Keriz/eeaic-2022-pll/pll.kicad_sch

## KiCad design pll.kicad_sch (2022-06-06)

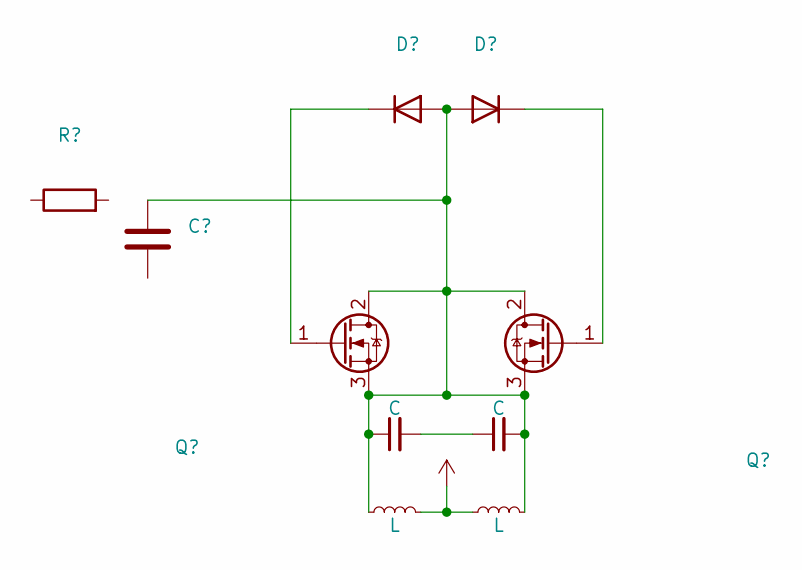
[picture p67: schematic pll.kicad_sch]

Parts:
C: (no value)
L: (no value)

Connections:
unnamed: C.1, C.2, L.1, L.2
unnamed: L.1, L.2
