Keriz/eeaic-2022-pll/PLL/PLL.kicad_sch

## KiCad design PLL/PLL.kicad_sch (2022-11-11, an earlier design)

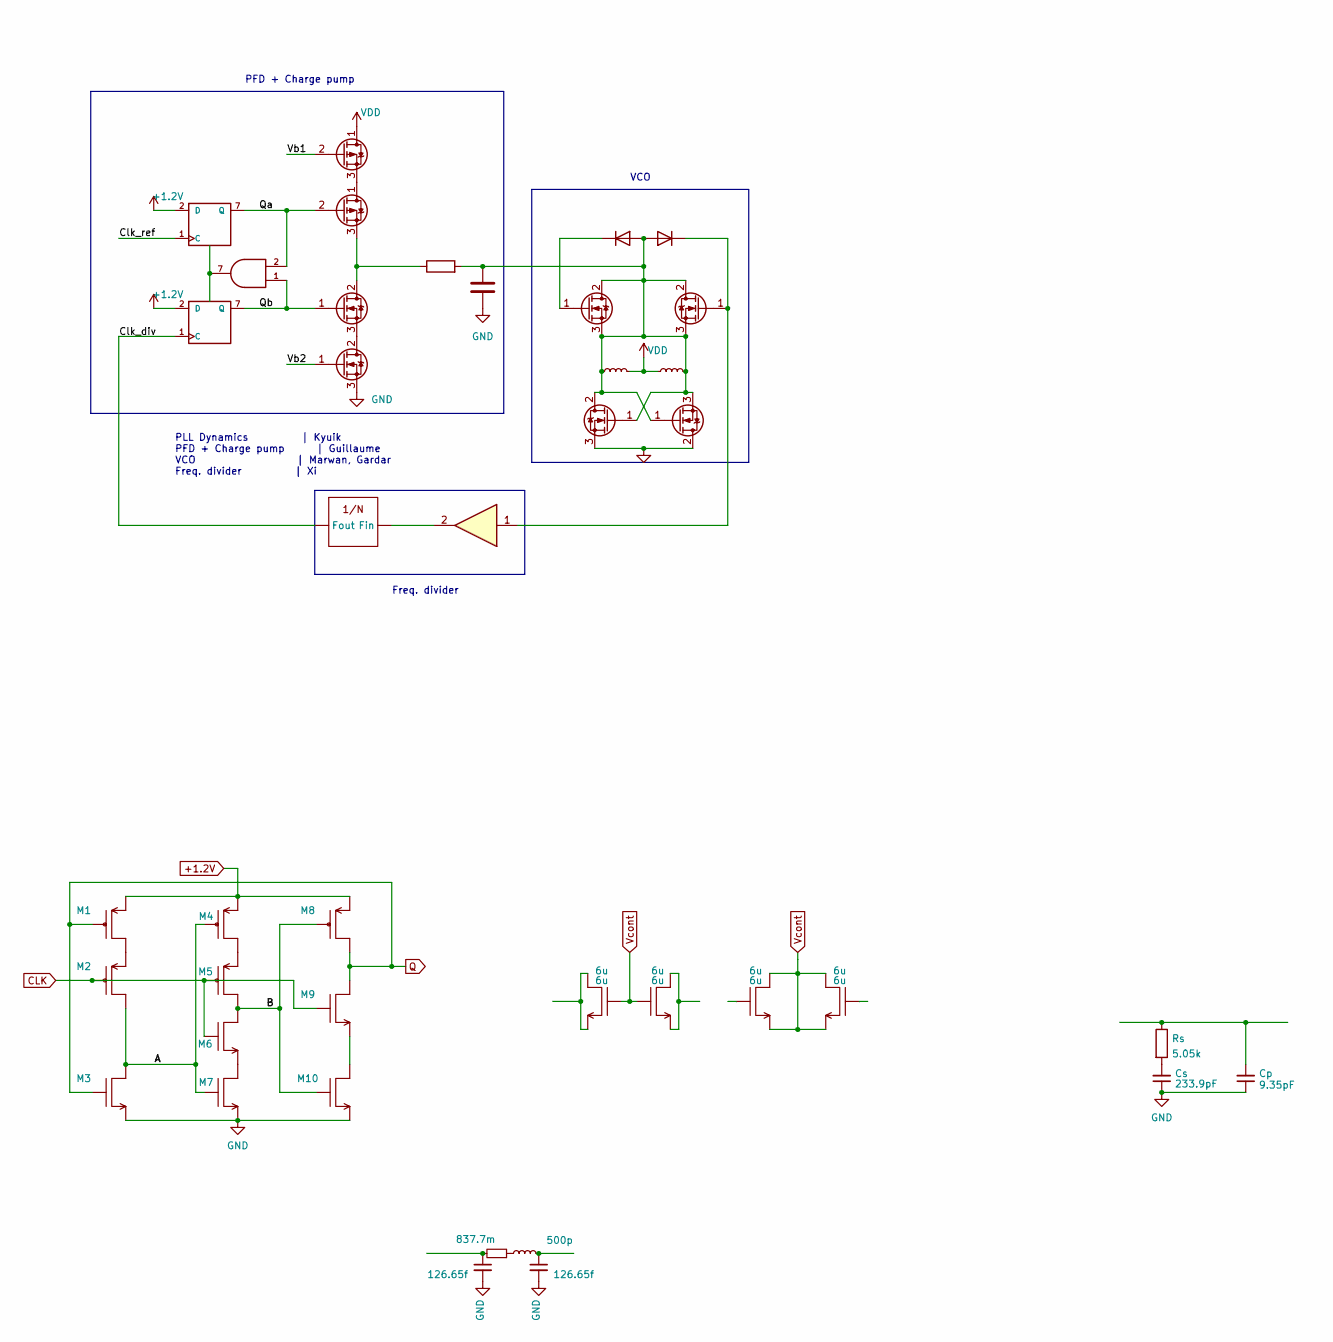
[picture p68: schematic PLL.kicad_sch, part in row 1, column 1]

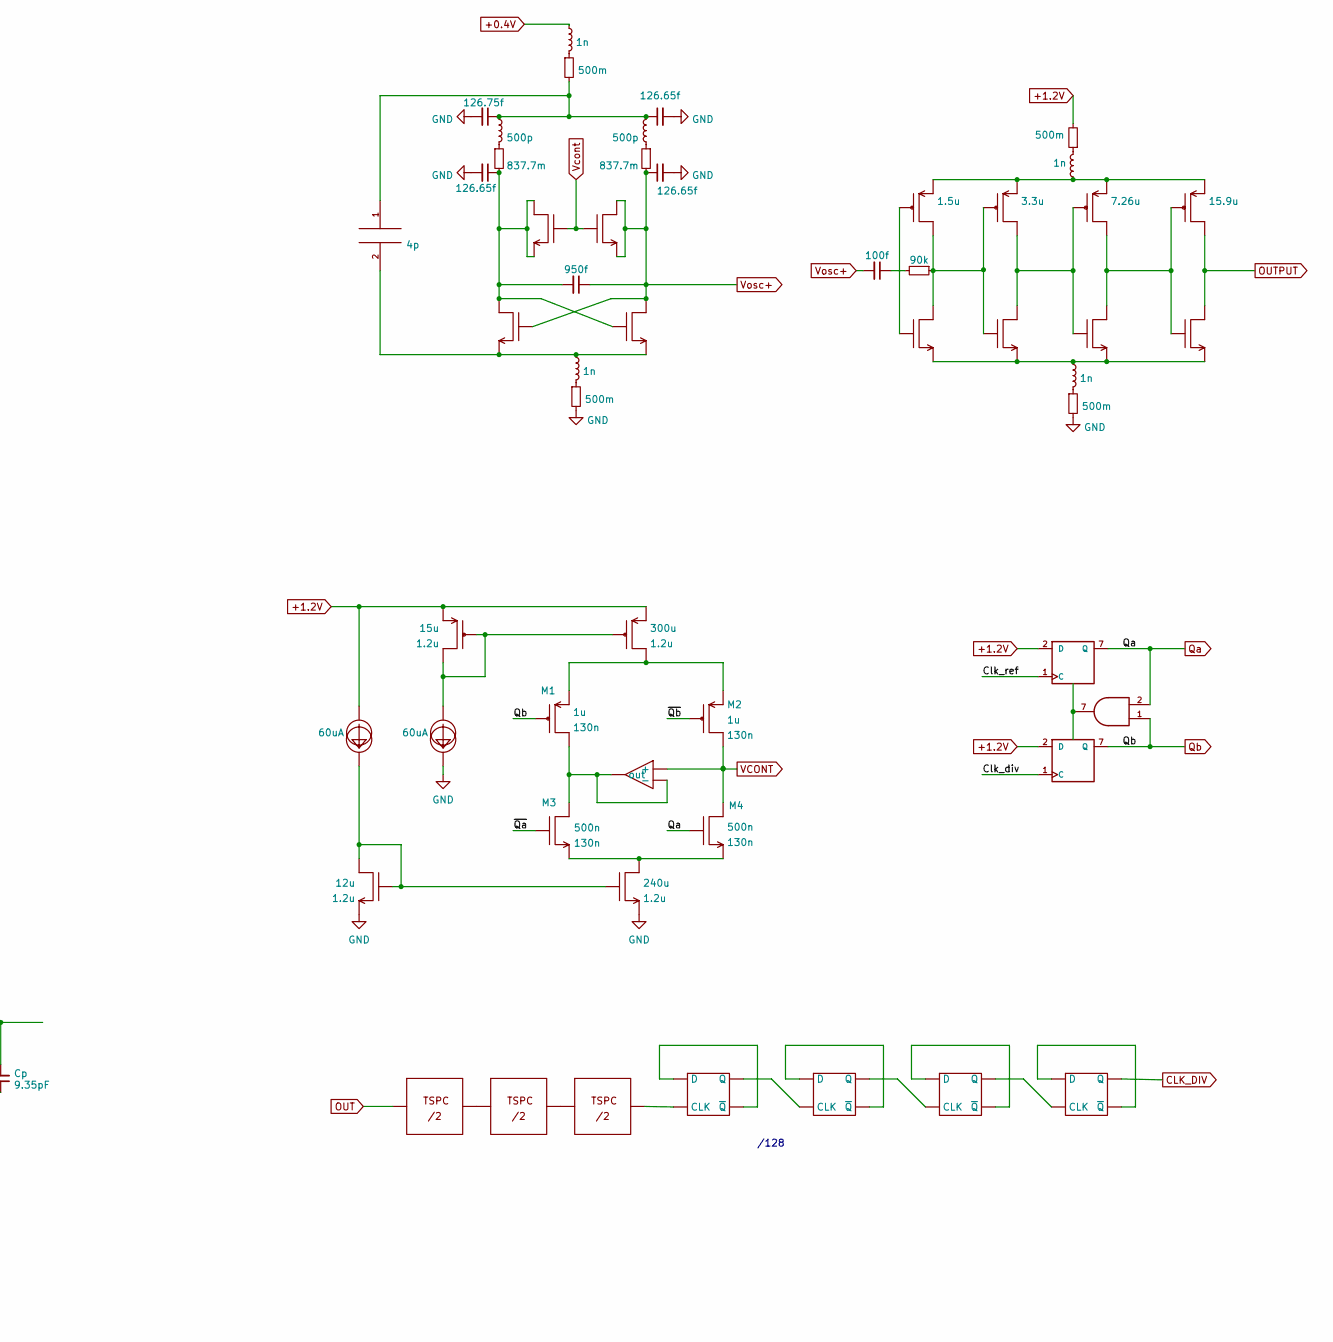
[picture p69: schematic PLL.kicad_sch, part in row 1, column 2]

Parts:
+1.2V: (no value)
Cp: 9.35pF
Cs: 233.9pF
GND: GND
M1, M2, M4, M5, M8, M12, M16: pch
M3, M6, M7, M9, M10, M11, M15: nch
Q: Q_PMOS_DGS
Rs: 5.05k
U1, U2: 60uA
U3: opamp
VDD: VDD

Connections:
+1.2V: M1., M4., M8., M12., M16., U1.
A: M2., M3., M4., M7.
B: M5., M6., M8., M10.
CLK: M2., M5., M6., M9.
GND: M3., M7., M10., M11., M15., U2.
unnamed: Cp.1, Cs.1
unnamed: Cp.2, Rs.1
unnamed: Cs.2, Rs.2
unnamed: M1., M2., M3., M16., U3.
unnamed: M4., M5.
unnamed: M6., M7.
unnamed: M9., M10.
unnamed: M11., M15., U1.
unnamed: M12., M16., U2.
unnamed: M3., M4., M15.
Q: M1., M3., M8., M9.
Qa: M4., Q.2 (G)
Qb: M1.
VCONT: M2., M4., U3.
~Qa: M3.
~Qb: M2.

Notes on the sheet:
Freq. divider
VCO
PFD + Charge pump
/128
PLL Dynamics | Kyuik PFD + Charge pump | Guillaume VCO | Marwan, Gardar Freq. divider | Xi
